kvalle/tinker-console/files/diylc/battery.png

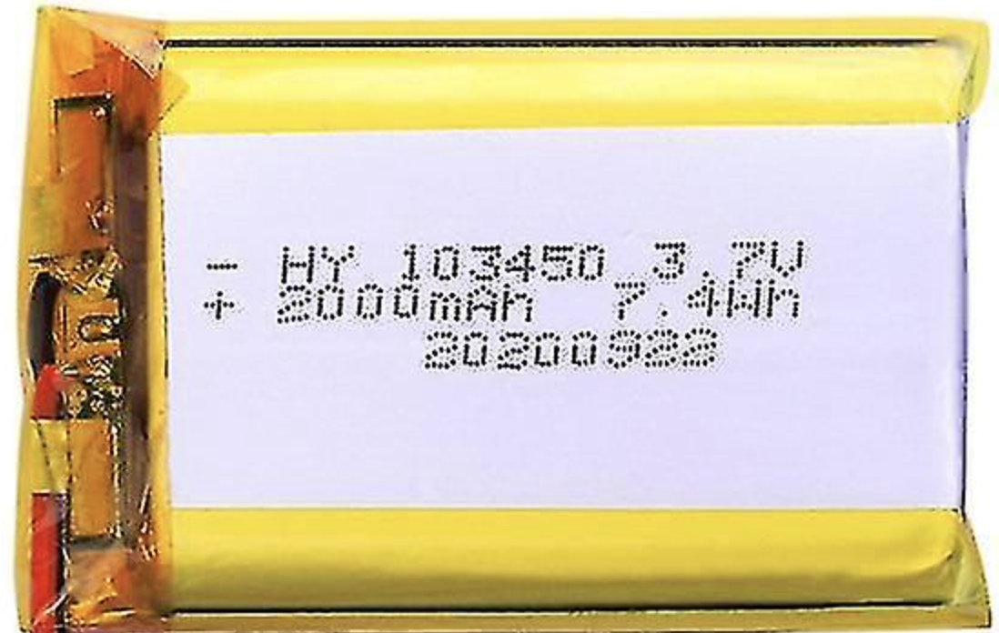
files/diylc/battery.png
