kvalle/tinker-console/files/diylc/MT3608.png

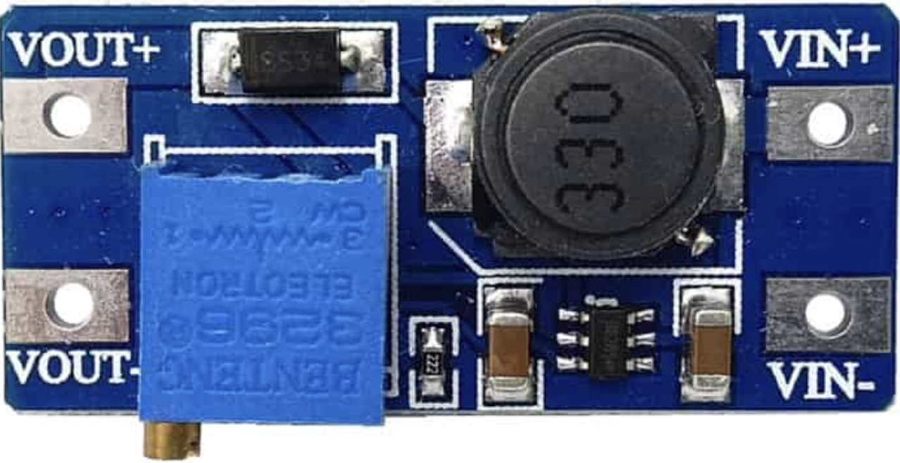
files/diylc/MT3608.png
