kvalle/tinker-console/files/diylc/TP4056.png

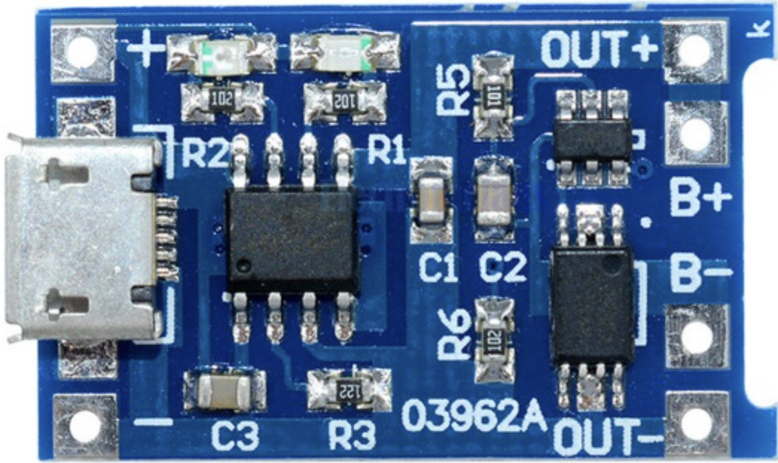
files/diylc/TP4056.png
