kvalle/tinker-console/code/include/Sounds.h

#ifndef SOUNDS_H
#define SOUNDS_H

#include "Buzzer.h"

extern const int marioCoin[][2];
extern const int marioPowerUp[][2];
extern const int marioOneUp[][2];
extern const int marioGameOver[][2];
extern const int marioFlagpole[][2];
extern const int marioThemeStart[][2];
extern const int marioThemeFull[][2];

extern const int fanfare[][2];

extern const int buttonPress[][2];
extern const int buttonPressDouble[][2];
extern const int buttonPress1[][2];
extern const int buttonPress2[][2];
extern const int buttonPress3[][2];
extern const int buttonPress4[][2];
extern const int buttonLongPress1[][2];
extern const int buttonLongPress2[][2];
extern const int buttonLongPress3[][2];
extern const int buttonLongPress4[][2];

extern const int popcornMelody[][2];

extern const int panelStartup[][2];

#endif // SOUNDS_H
